richardli03/record-music-visualizer/assets/imgs/365_all_data.png

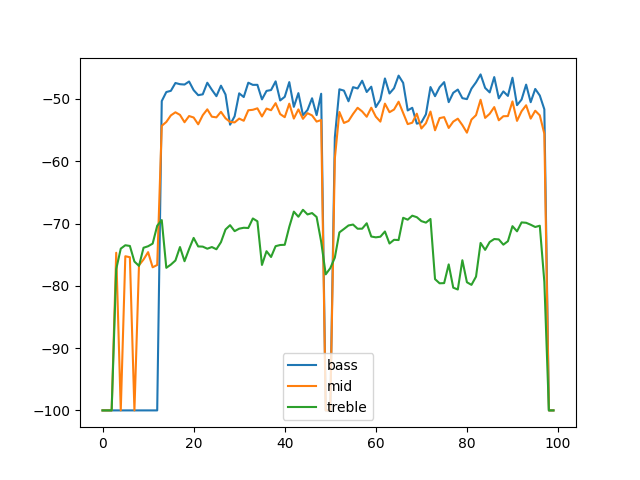
assets/imgs/365_all_data.png
