richardli03/record-music-visualizer/assets/imgs/365_osc.png

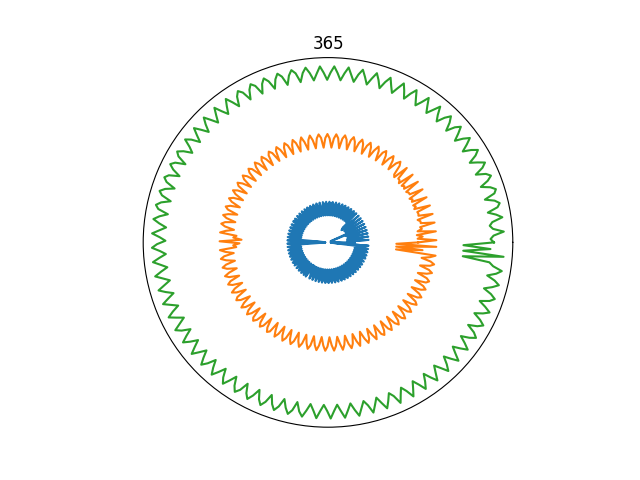
assets/imgs/365_osc.png
