richardli03/record-music-visualizer/assets/imgs/a_little_night_osc.png

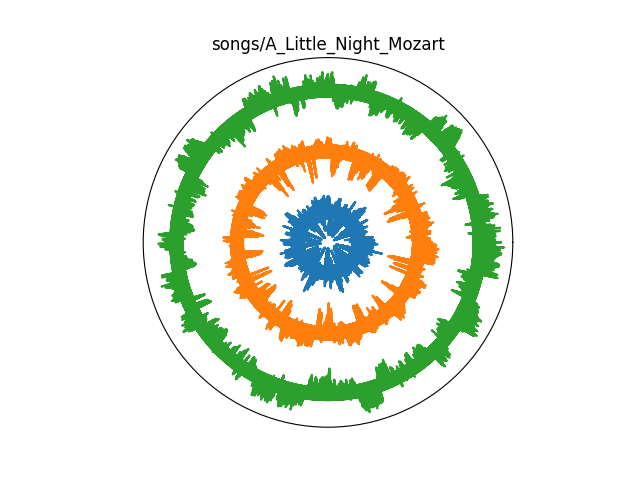
assets/imgs/a_little_night_osc.png
