richardli03/record-music-visualizer/assets/imgs/bass_over_time.png

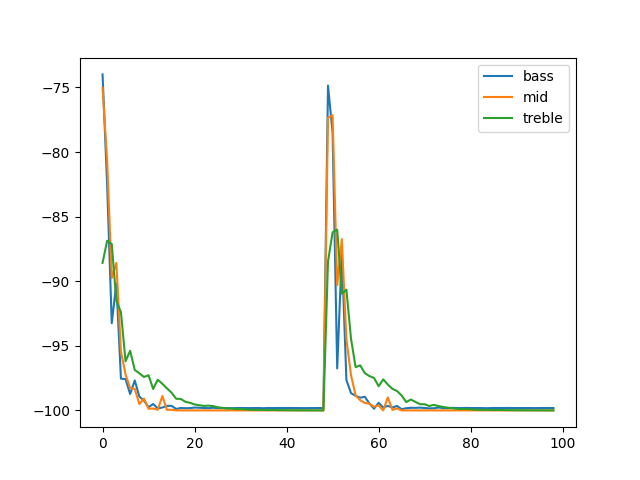
assets/imgs/bass_over_time.png
