richardli03/record-music-visualizer/assets/imgs/heres_to_us_denser_osc.png

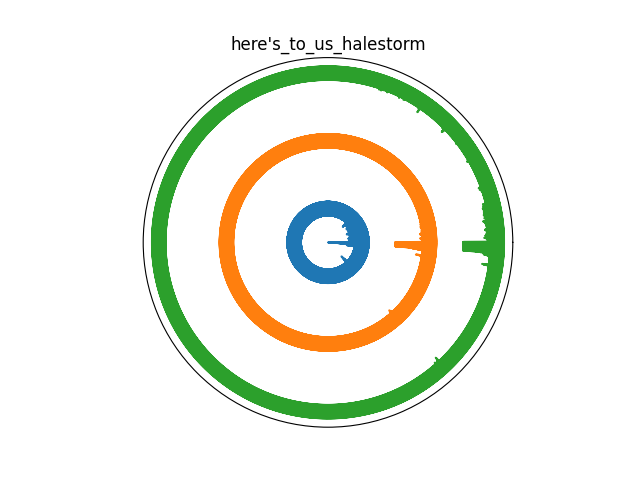
assets/imgs/heres_to_us_denser_osc.png
