richardli03/record-music-visualizer/assets/imgs/librosa/bass.png

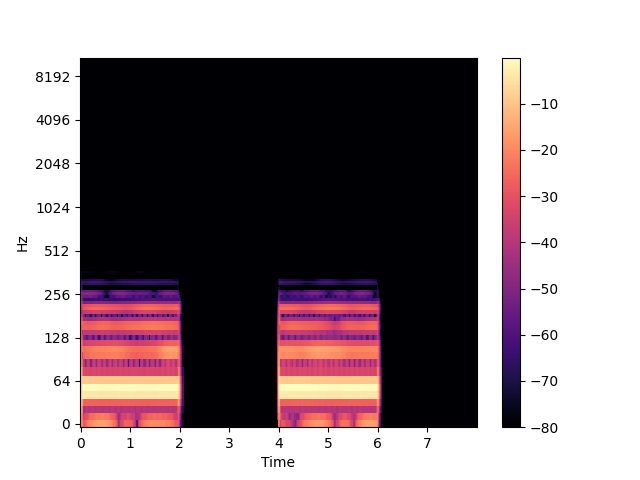
assets/imgs/librosa/bass.png
