richardli03/record-music-visualizer/assets/imgs/librosa/mids.png

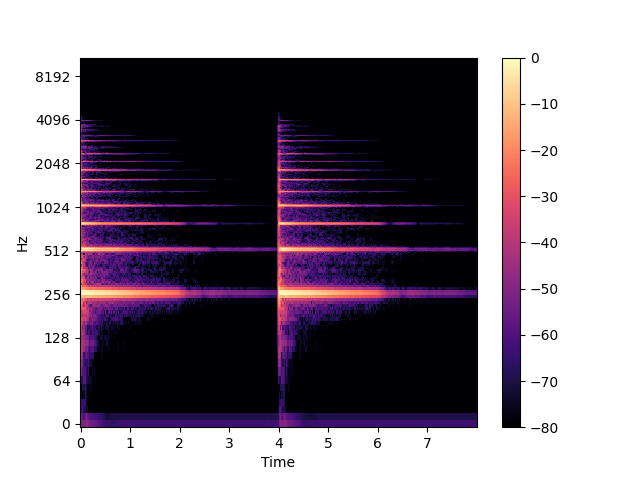
assets/imgs/librosa/mids.png
