richardli03/record-music-visualizer/assets/imgs/librosa/frequency_band_test.png

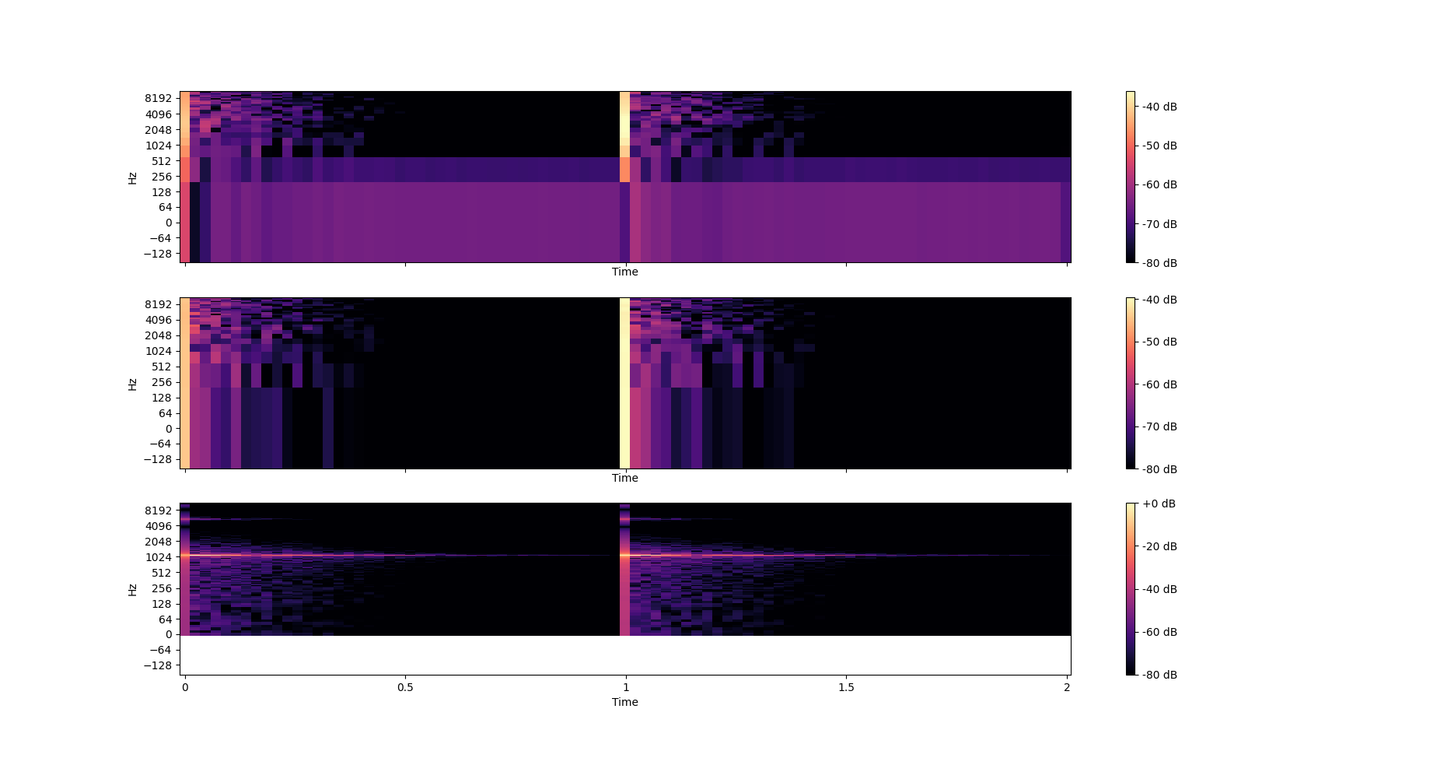
assets/imgs/librosa/frequency_band_test.png
